Stustup/C-Audio-BHOA/Hardware/KiCAD/BHOA/Symbols/Amp Symbol.png

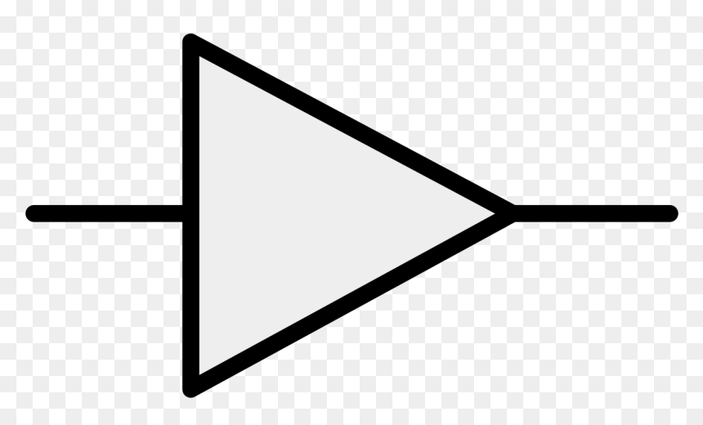
Hardware/KiCAD/BHOA/Symbols/Amp Symbol.png
