Stustup/C-Audio-BHOA/PCB whole.png

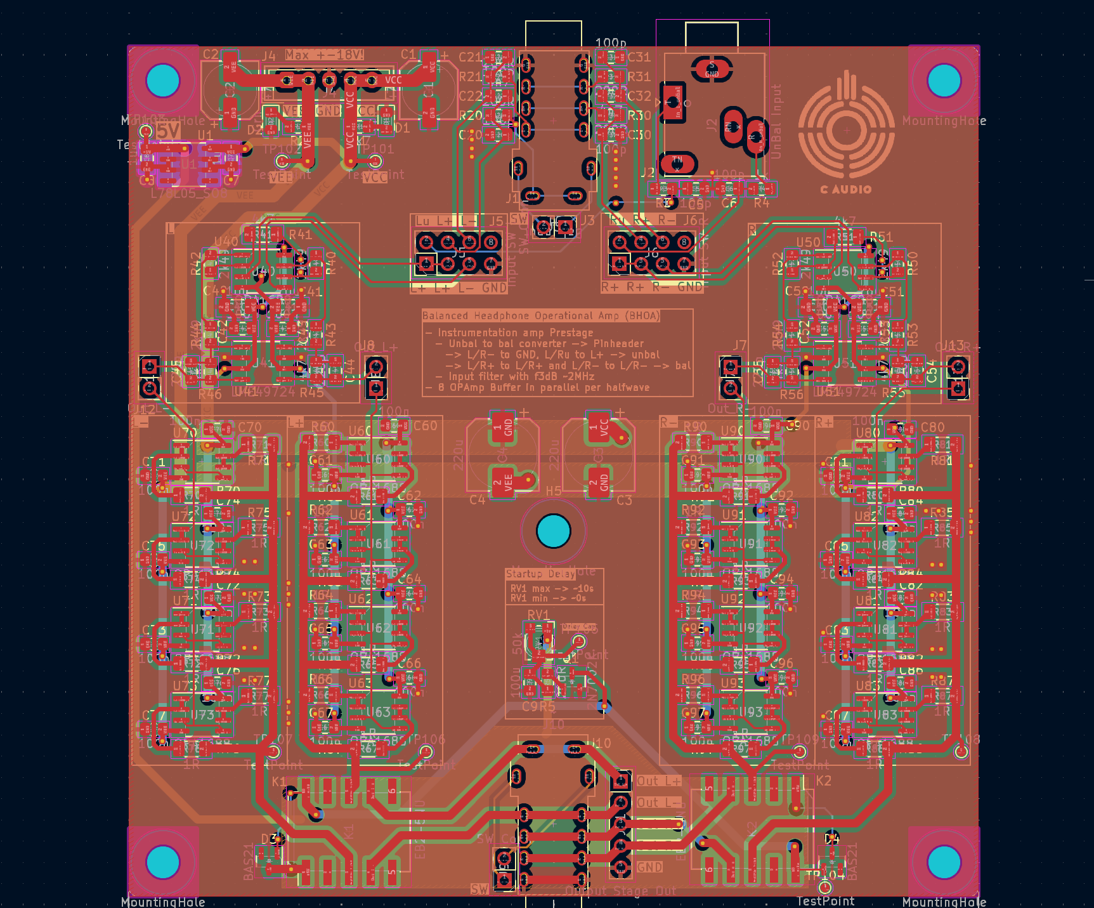
PCB whole.png
